AthemiS13/NeoGrip/Config/ALVR/ALVRSETUP2.png

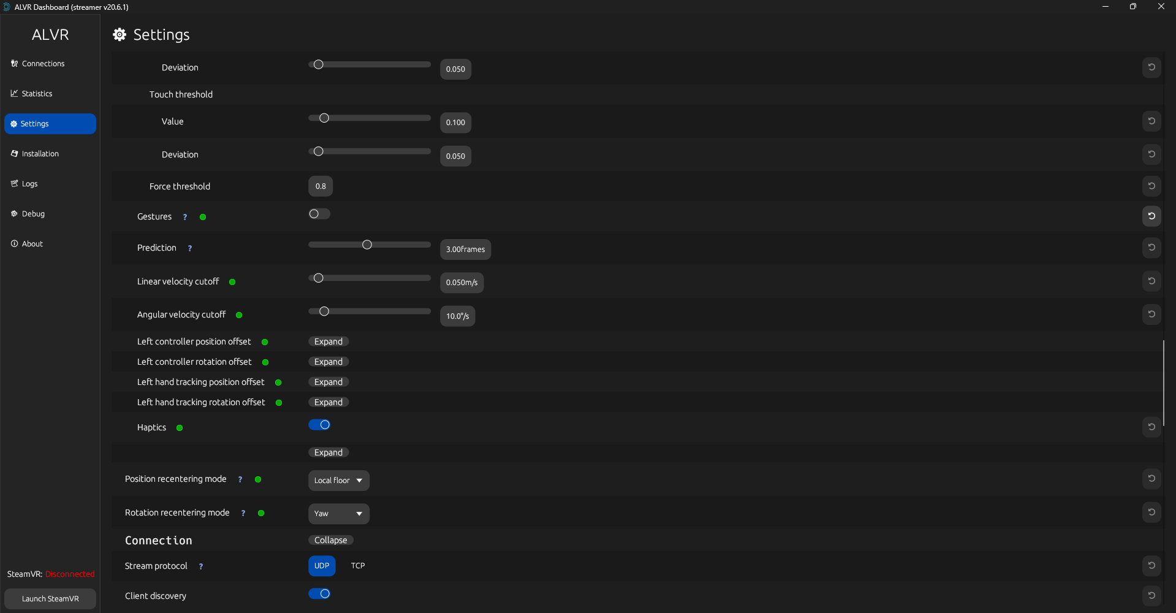
Config/ALVR/ALVRSETUP2.png
